AnnaJinK/AVR_FLASHER/PCB/img/2.png

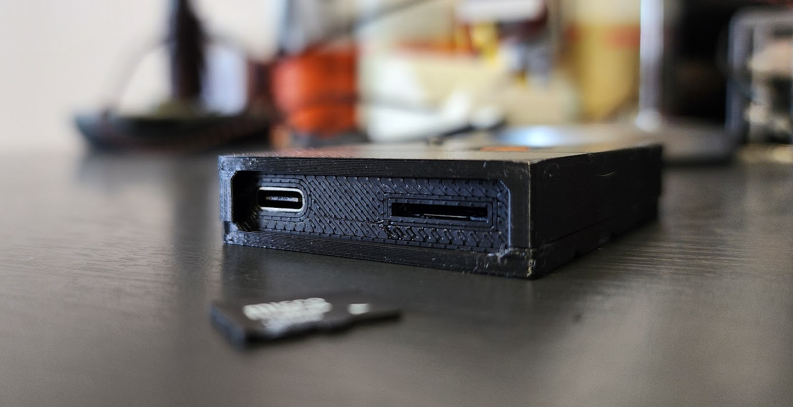
PCB/img/2.png
